fhnw-ip12-24vt/gletschery-docu/software(sad)/sad/12_glossary.adoc

== Glossar

[role="arc42help"]
****
.Inhalt
Die wesentlichen fachlichen und technischen Begriffe, die Stakeholder im Zusammenhang mit dem System verwenden.

Nutzen Sie das Glossar ebenfalls als Übersetzungsreferenz, falls Sie in mehrsprachigen Teams arbeiten.

.Motivation
Sie sollten relevante Begriffe klar definieren, so dass alle Beteiligten

* diese Begriffe identisch verstehen, und
* vermeiden, mehrere Begriffe für die gleiche Sache zu haben.

.Form
* Zweispaltige Tabelle mit <Begriff> und <Definition>
* Eventuell weitere Spalten mit Übersetzungen, falls notwendig.

.Weiterführende Informationen

Siehe https://docs.arc42.org/section-12/[Glossar] in der online-Dokumentation (auf Englisch!).

****

[cols="e,2e" options="header"]
|===
|Begriff |Definition

|<Begriff-1>
|<Definition-1>

|<Begriff-2
|<Definition-2>
|===
