fhnw-ip12-24vt/gletschery-docu/Files/generalImages/backgroundImage.png

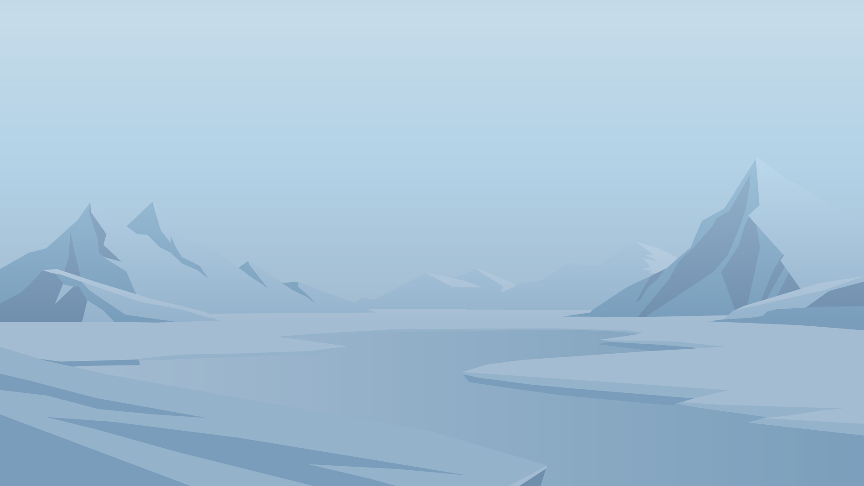
Files/generalImages/backgroundImage.png
