fhnw-ip12-24vt/gletschery-docu/Files/generalImages/englishFlag.png

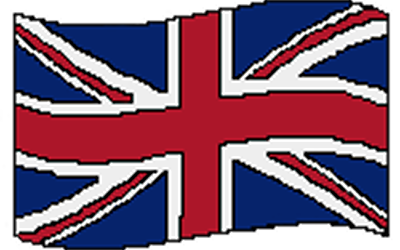
Files/generalImages/englishFlag.png
