fhnw-ip12-24vt/gletschery-docu/Files/generalImages/frenchFlag.png

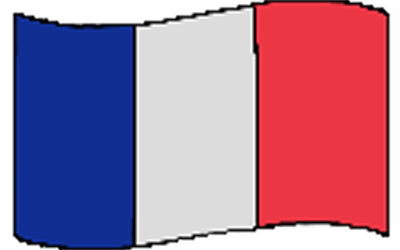
Files/generalImages/frenchFlag.png
