fhnw-ip12-24vt/gletschery-docu/Files/generalImages/germanFlag.png

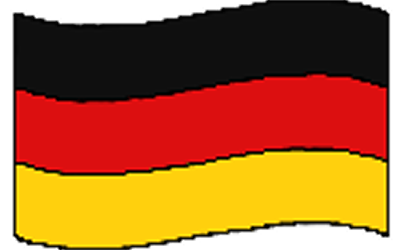
Files/generalImages/germanFlag.png
