fhnw-ip12-24vt/gletschery-docu/Files/generalImages/introductionDE.png

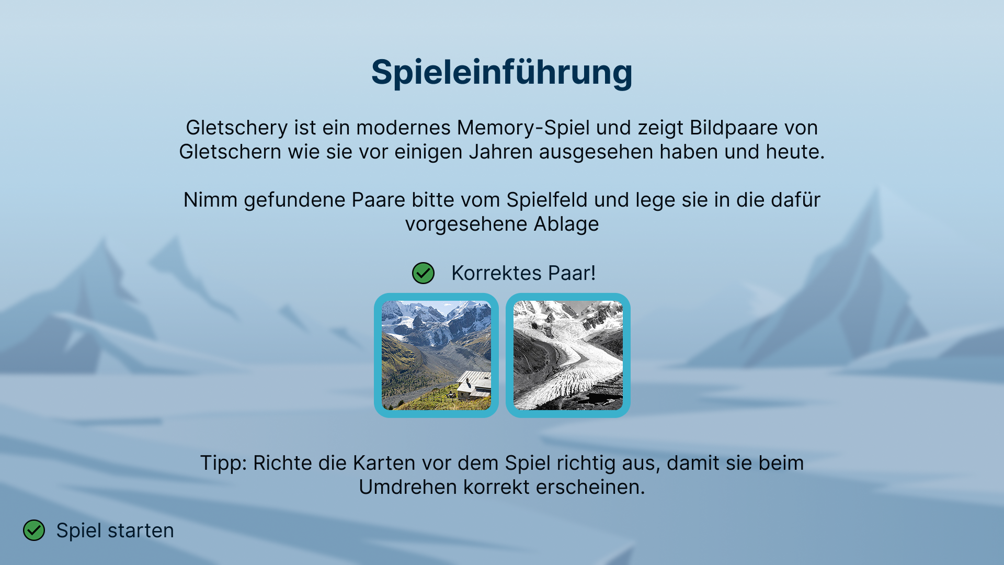
Files/generalImages/introductionDE.png
