fhnw-ip12-24vt/gletschery-docu/Files/generalImages/introductionEN.png

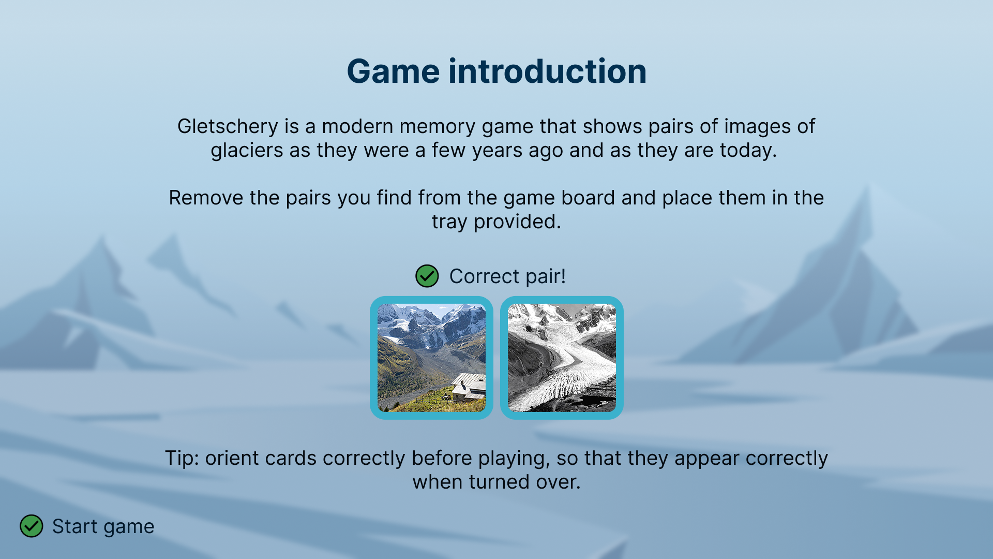
Files/generalImages/introductionEN.png
