fhnw-ip12-24vt/gletschery-docu/Files/generalImages/murmeltier.png

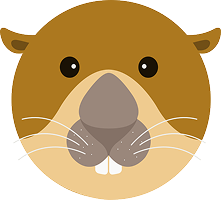
Files/generalImages/murmeltier.png
