fhnw-ip12-24vt/gletschery-docu/Files/generalImages/steinbock.png

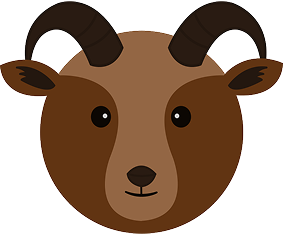
Files/generalImages/steinbock.png
