fhnw-ip12-24vt/gletschery-docu/Files/gletscherImages/Aletschgletscher-A.png

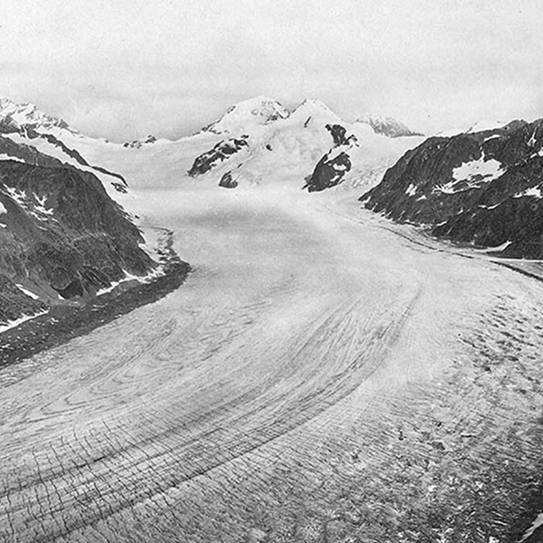
Files/gletscherImages/Aletschgletscher-A.png
