fhnw-ip12-24vt/gletschery-docu/Files/gletscherImages/Aletschgletscher-B.png

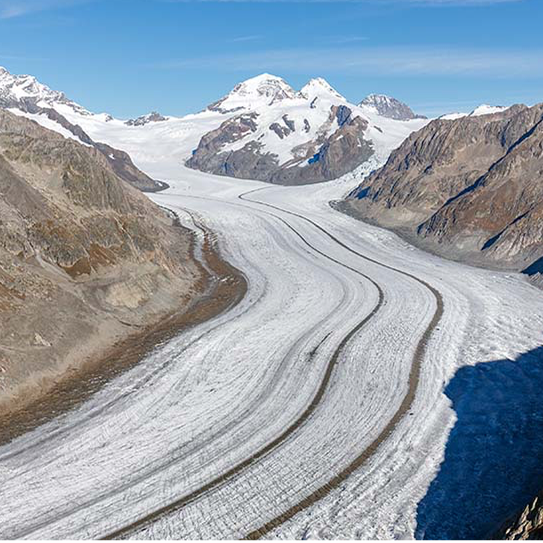
Files/gletscherImages/Aletschgletscher-B.png
