fhnw-ip12-24vt/gletschery-docu/Files/gletscherImages/Fieschergletscher-A.png

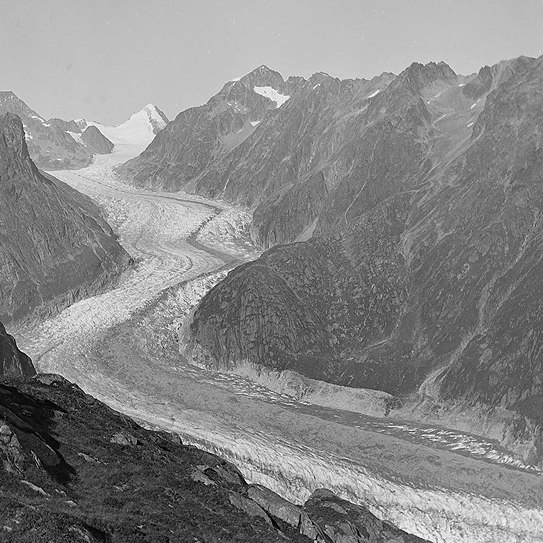
Files/gletscherImages/Fieschergletscher-A.png
