fhnw-ip12-24vt/gletschery-docu/Files/gletscherImages/Fieschergletscher-B.png

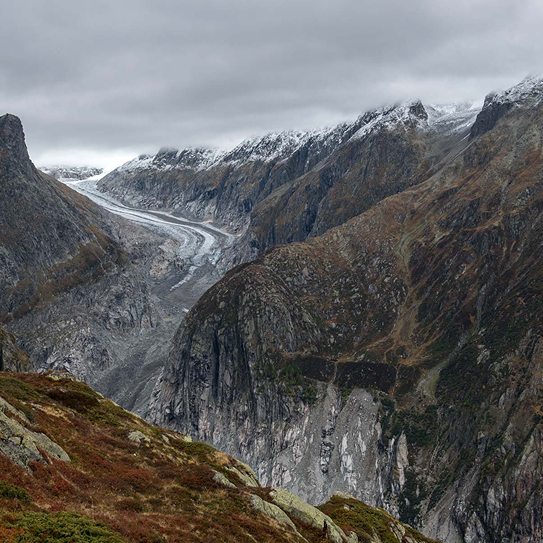
Files/gletscherImages/Fieschergletscher-B.png
