fhnw-ip12-24vt/gletschery-docu/Files/gletscherImages/Gornergletscher-A.png

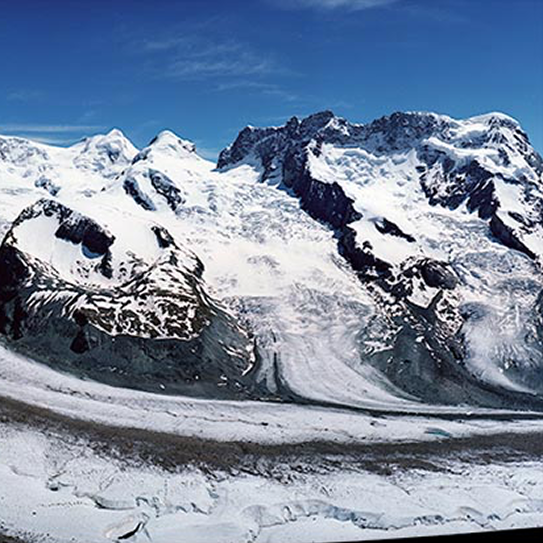
Files/gletscherImages/Gornergletscher-A.png
