fhnw-ip12-24vt/gletschery-docu/Files/gletscherImages/Gornergletscher-B.png

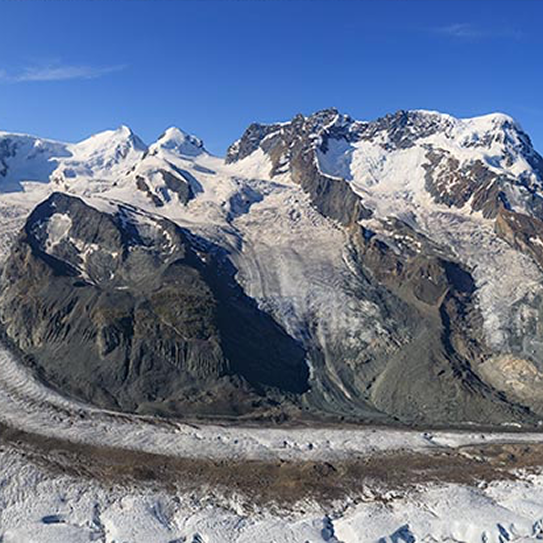
Files/gletscherImages/Gornergletscher-B.png
