fhnw-ip12-24vt/gletschery-docu/Files/gletscherImages/Persgletscher-A.png

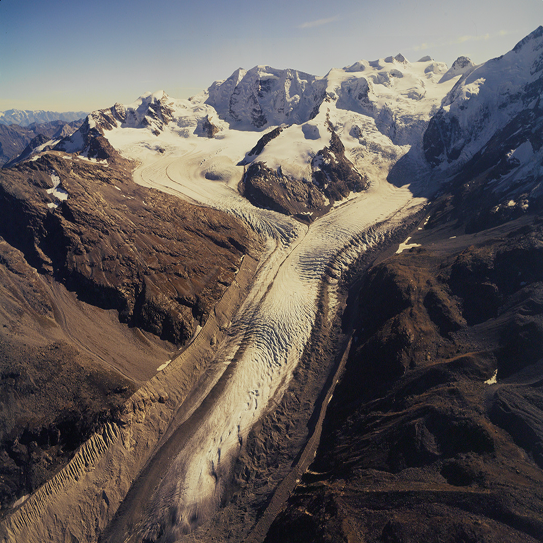
Files/gletscherImages/Persgletscher-A.png
