fhnw-ip12-24vt/gletschery-docu/Files/gletscherImages/Persgletscher-B.png

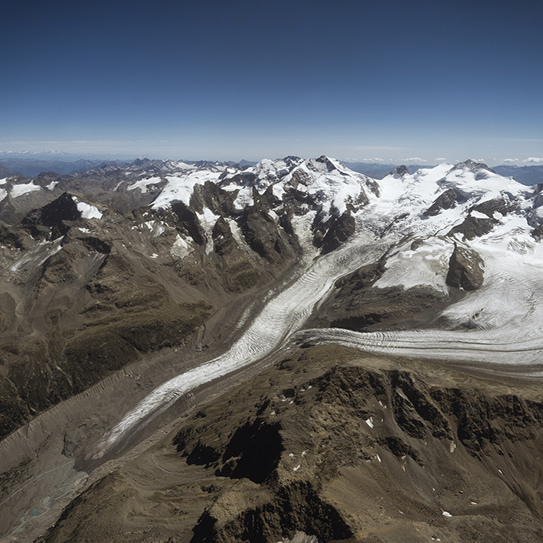
Files/gletscherImages/Persgletscher-B.png
