fhnw-ip12-24vt/gletschery-docu/Files/gletscherImages/Pizolgletscher-A.png

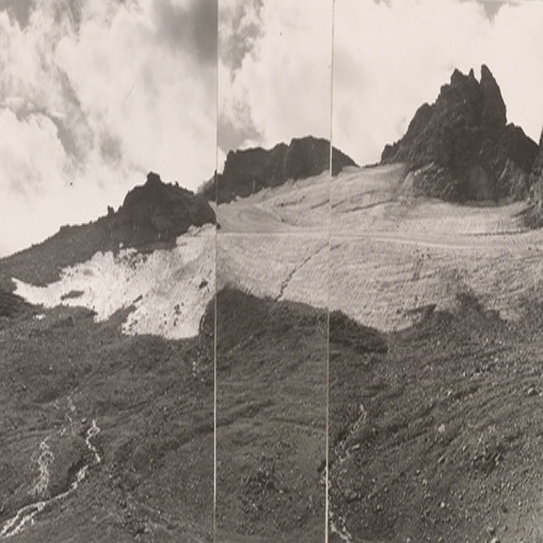
Files/gletscherImages/Pizolgletscher-A.png
