fhnw-ip12-24vt/gletschery-docu/Files/gletscherImages/Pizolgletscher-B.png

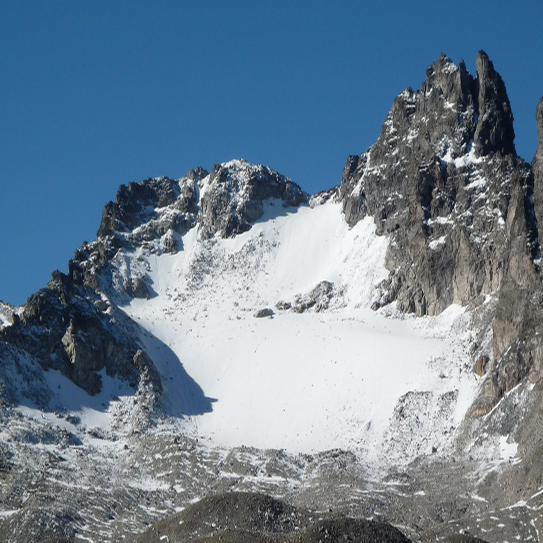
Files/gletscherImages/Pizolgletscher-B.png
