fhnw-ip12-24vt/gletschery-docu/Files/gletscherImages/Rhonegletscher-A.png

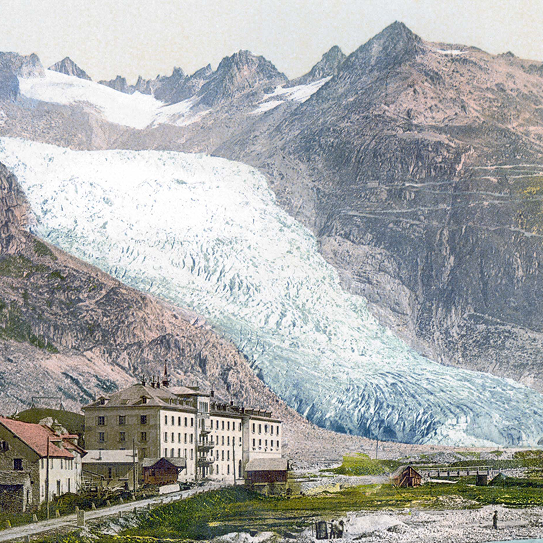
Files/gletscherImages/Rhonegletscher-A.png
