fhnw-ip12-24vt/gletschery-docu/Files/gletscherImages/Rhonegletscher-B.png

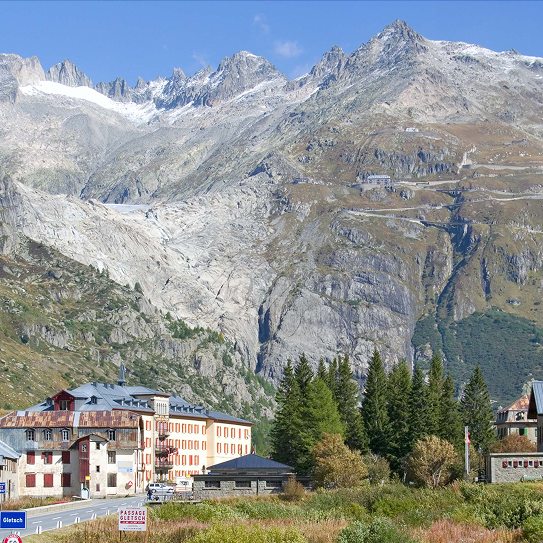
Files/gletscherImages/Rhonegletscher-B.png
