fhnw-ip12-24vt/gletschery-docu/Files/gletscherImages/Riedgletscher-A.png

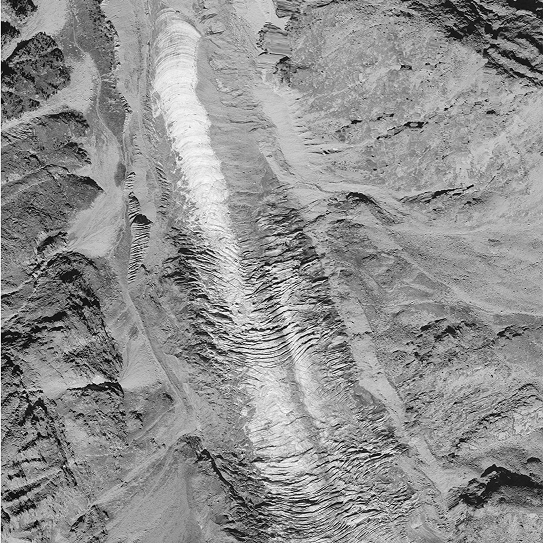
Files/gletscherImages/Riedgletscher-A.png
