fhnw-ip12-24vt/gletschery-docu/Files/gletscherImages/Riedgletscher-B.png

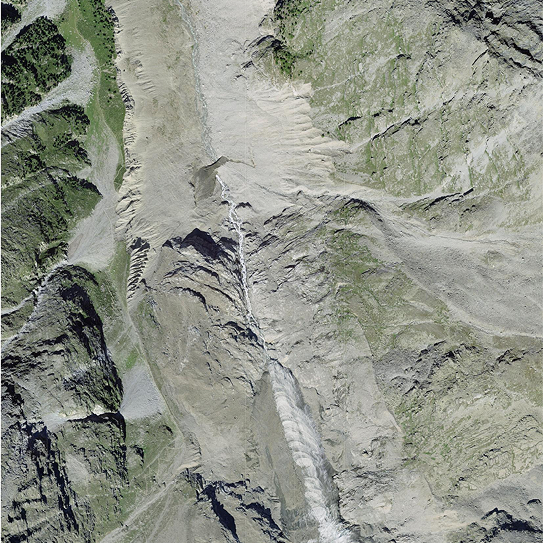
Files/gletscherImages/Riedgletscher-B.png
