fhnw-ip12-24vt/gletschery-docu/Files/gletscherImages/Roseggletscher-A.png

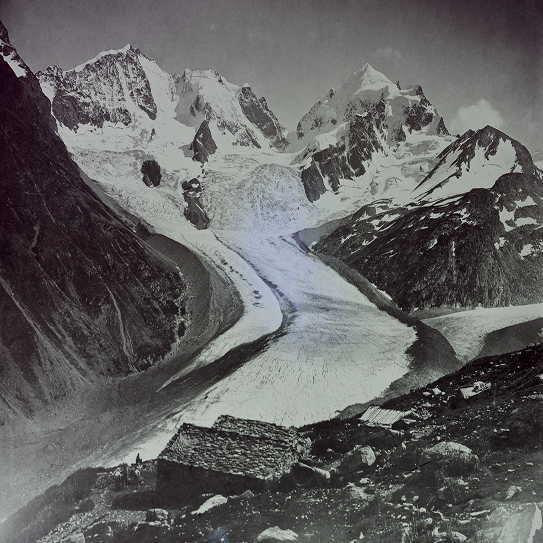
Files/gletscherImages/Roseggletscher-A.png
