fhnw-ip12-24vt/gletschery-docu/Files/gletscherImages/Roseggletscher-B.png

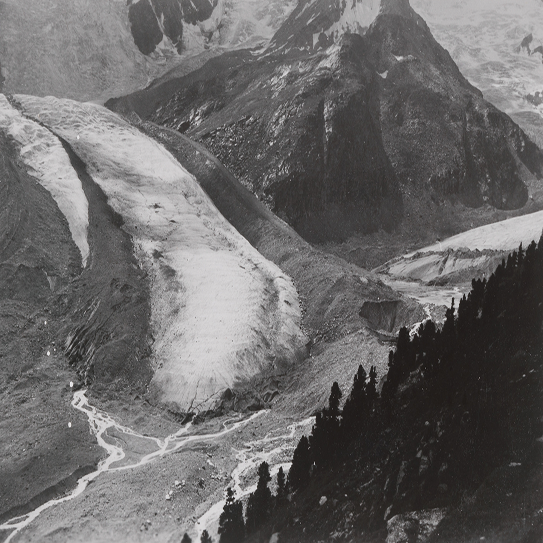
Files/gletscherImages/Roseggletscher-B.png
