fhnw-ip12-24vt/gletschery-docu/Files/gletscherImages/Tiefengletscher-A.png

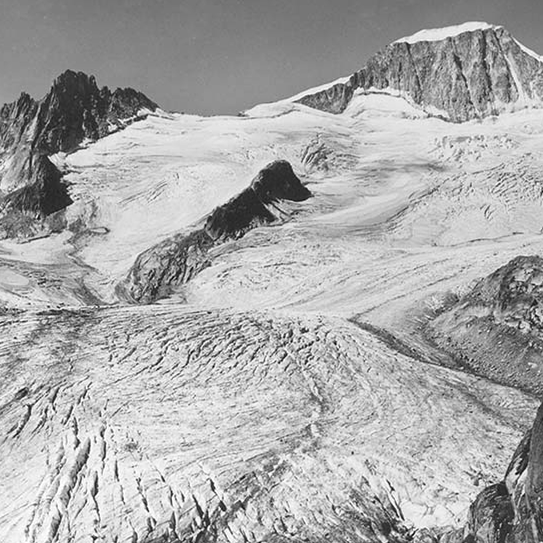
Files/gletscherImages/Tiefengletscher-A.png
