fhnw-ip12-24vt/gletschery-docu/Files/gletscherImages/Tiefengletscher-B.png

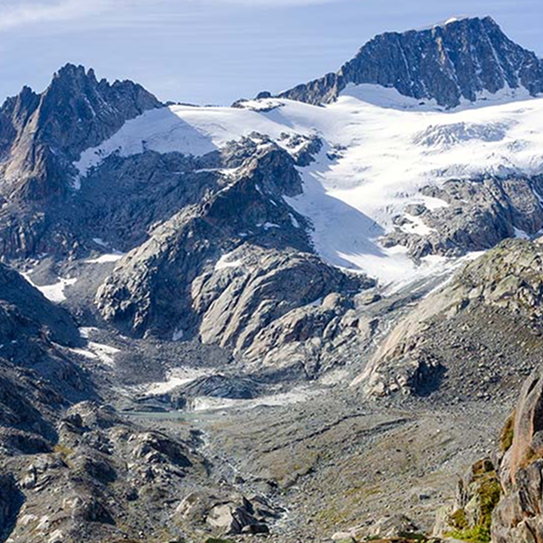
Files/gletscherImages/Tiefengletscher-B.png
