fhnw-ip12-24vt/gletschery-docu/Files/gletscherImages/Trientgletscher-A.png

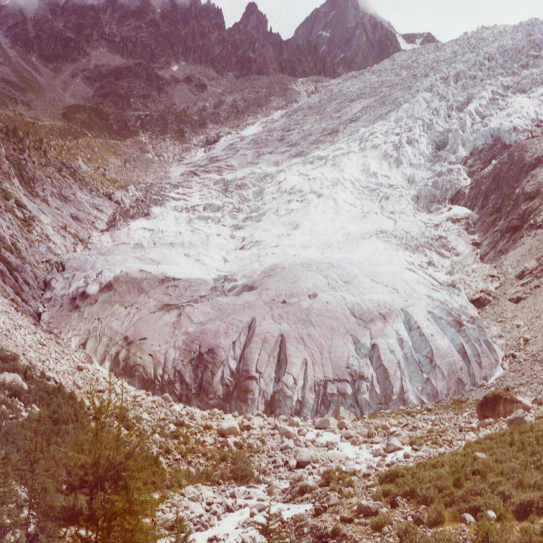
Files/gletscherImages/Trientgletscher-A.png
