fhnw-ip12-24vt/gletschery-docu/Files/gletscherImages/Trientgletscher-B.png

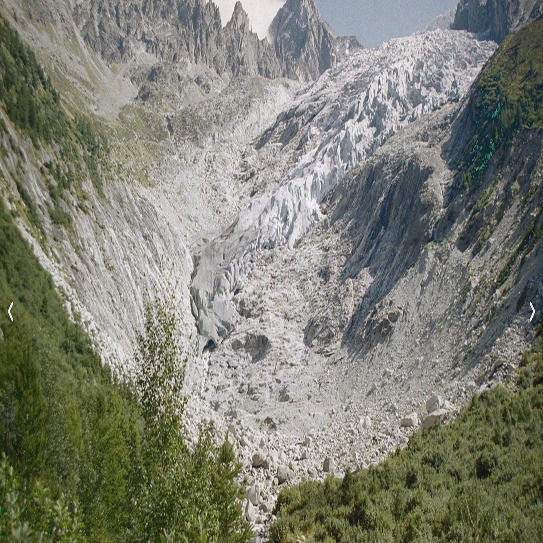
Files/gletscherImages/Trientgletscher-B.png
