fhnw-ip12-24vt/gletschery-docu/Files/gletscherImages/Triftgletscher-A.png

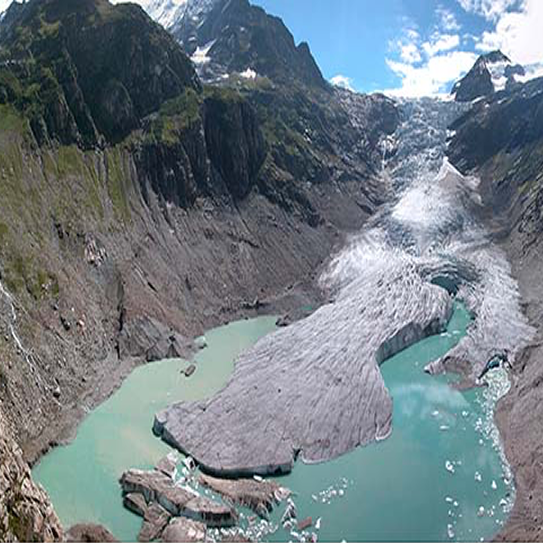
Files/gletscherImages/Triftgletscher-A.png
