fhnw-ip12-24vt/gletschery-docu/Files/gletscherImages/Triftgletscher-B.png

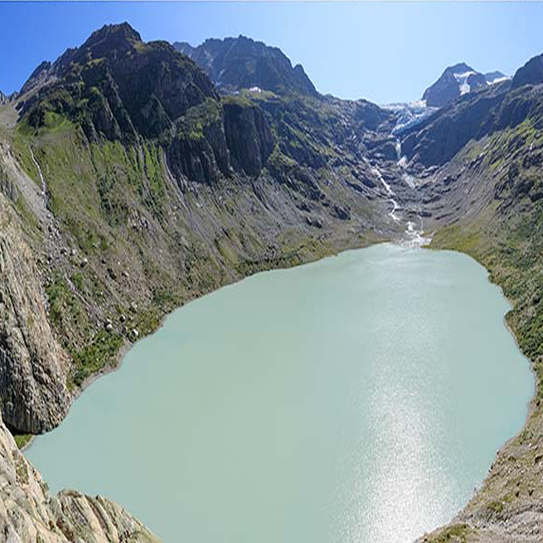
Files/gletscherImages/Triftgletscher-B.png
