fhnw-ip12-24vt/gletschery-docu/Files/gletscherImages/Tschierva-A.png

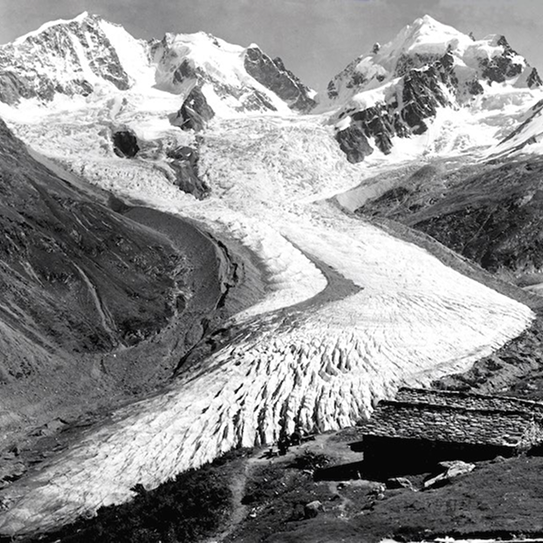
Files/gletscherImages/Tschierva-A.png
