fhnw-ip12-24vt/gletschery-docu/Files/gletscherImages/Tschierva-B.png

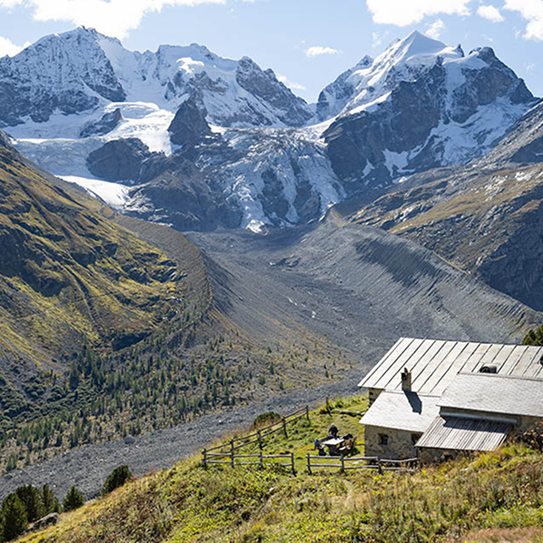
Files/gletscherImages/Tschierva-B.png
