fhnw-ip12-24vt/gletschery-docu/software(sad)/images/06-Flussdiagram-Run Methode.png

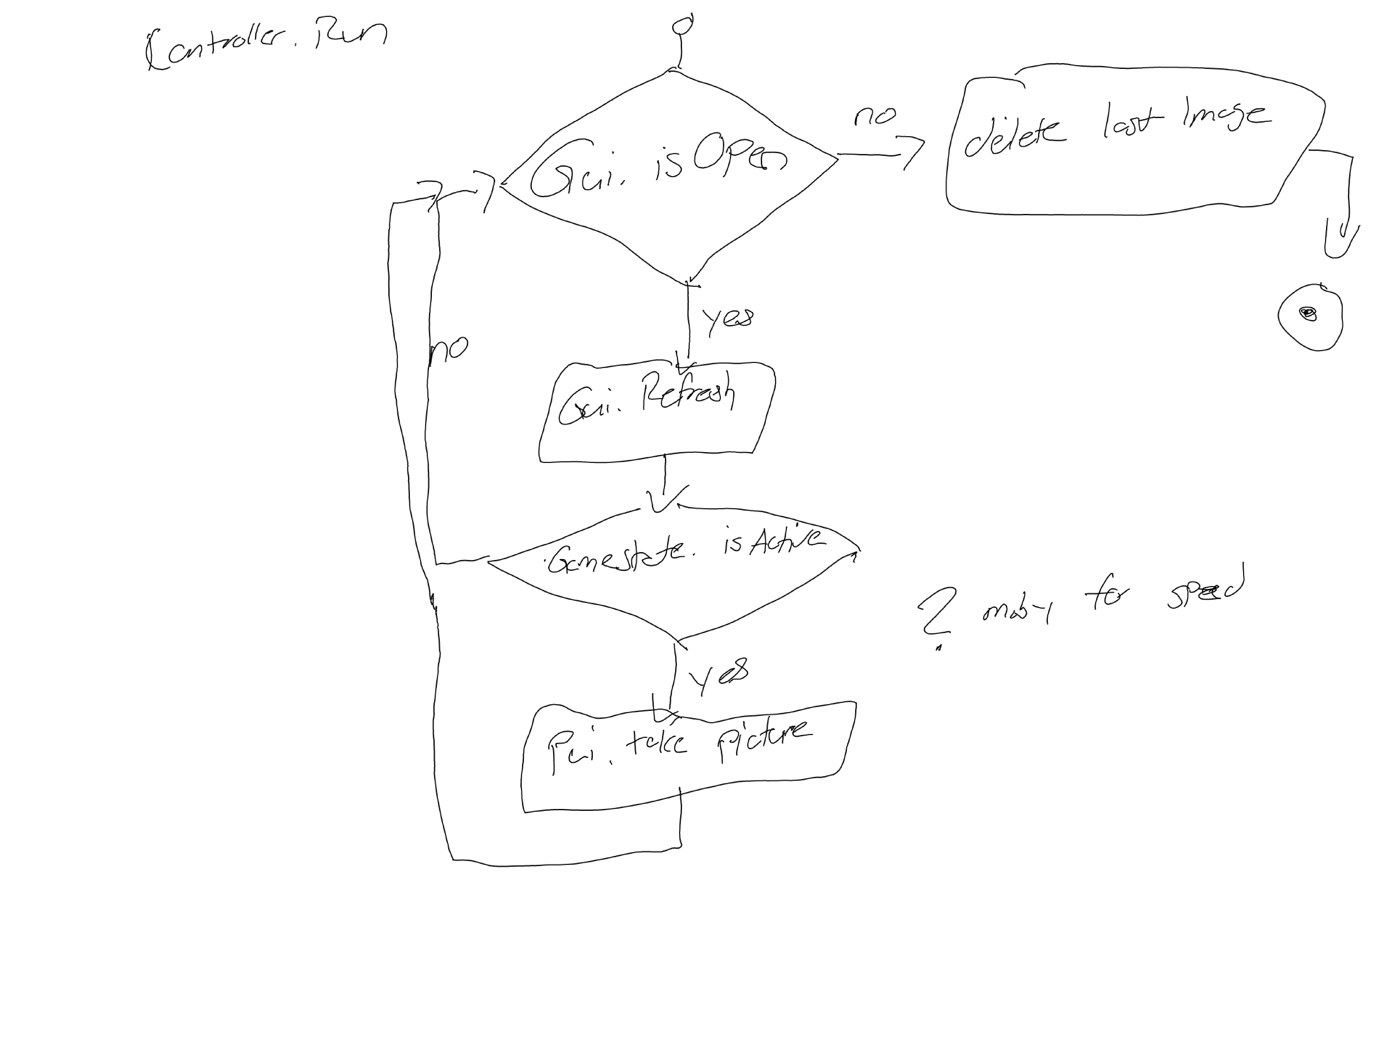
software(sad)/images/06-Flussdiagram-Run Methode.png
