fhnw-ip12-24vt/gletschery-docu/software(sad)/images/06-Sequenz Diagram Startup.png

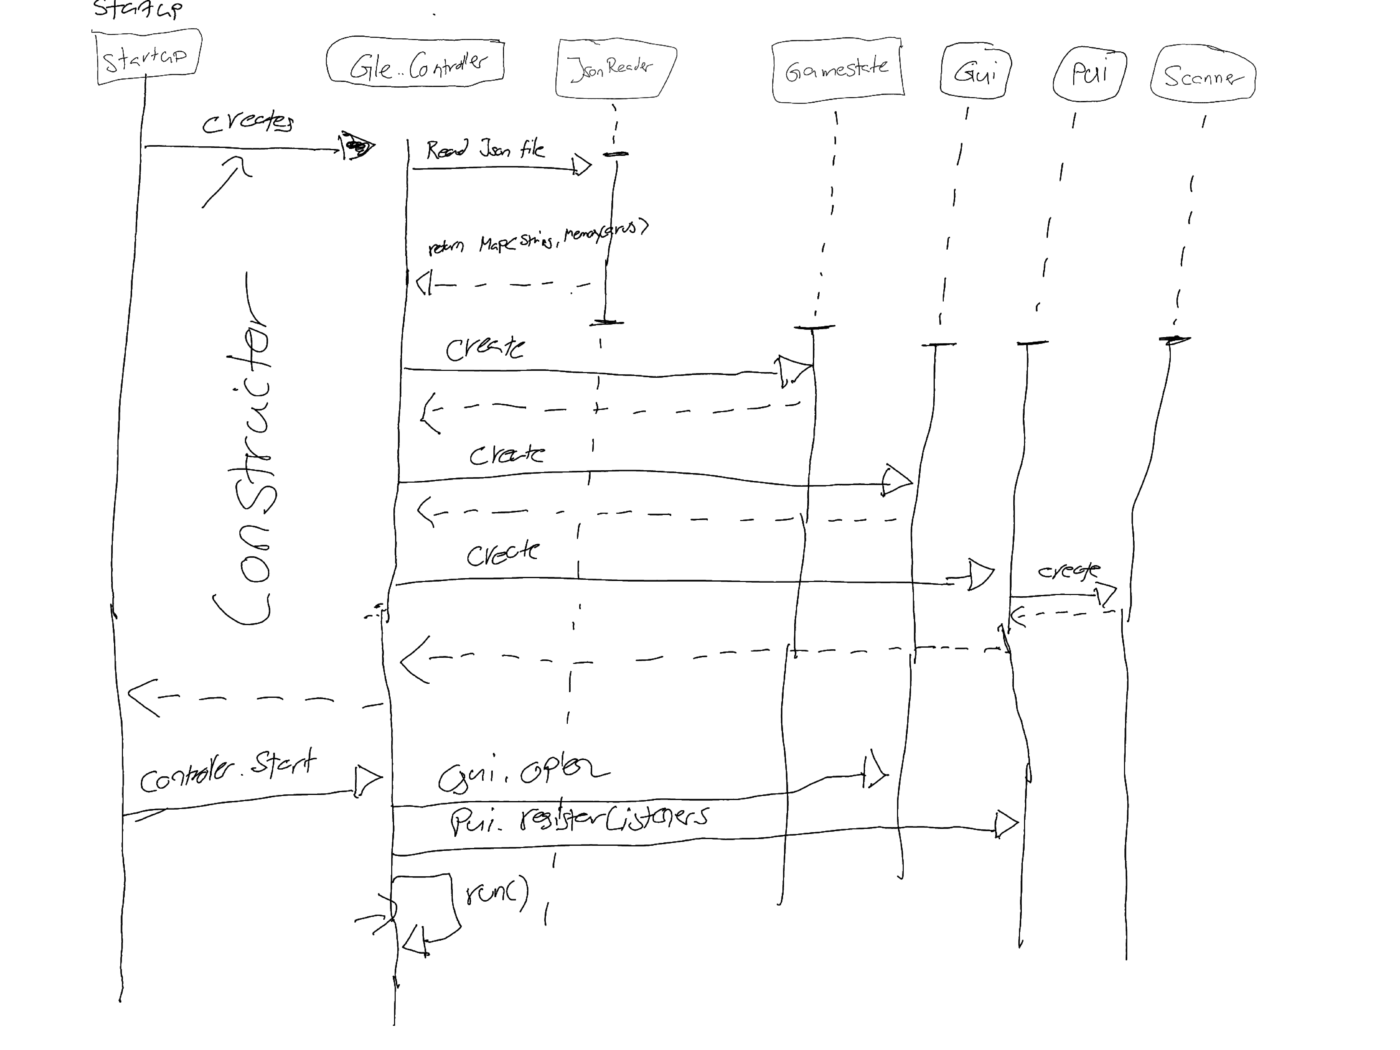
software(sad)/images/06-Sequenz Diagram Startup.png
