fhnw-ip12-24vt/gletschery-docu/software(sad)/images/06-Sequenz Diagram-Buttonpress(Scan).png

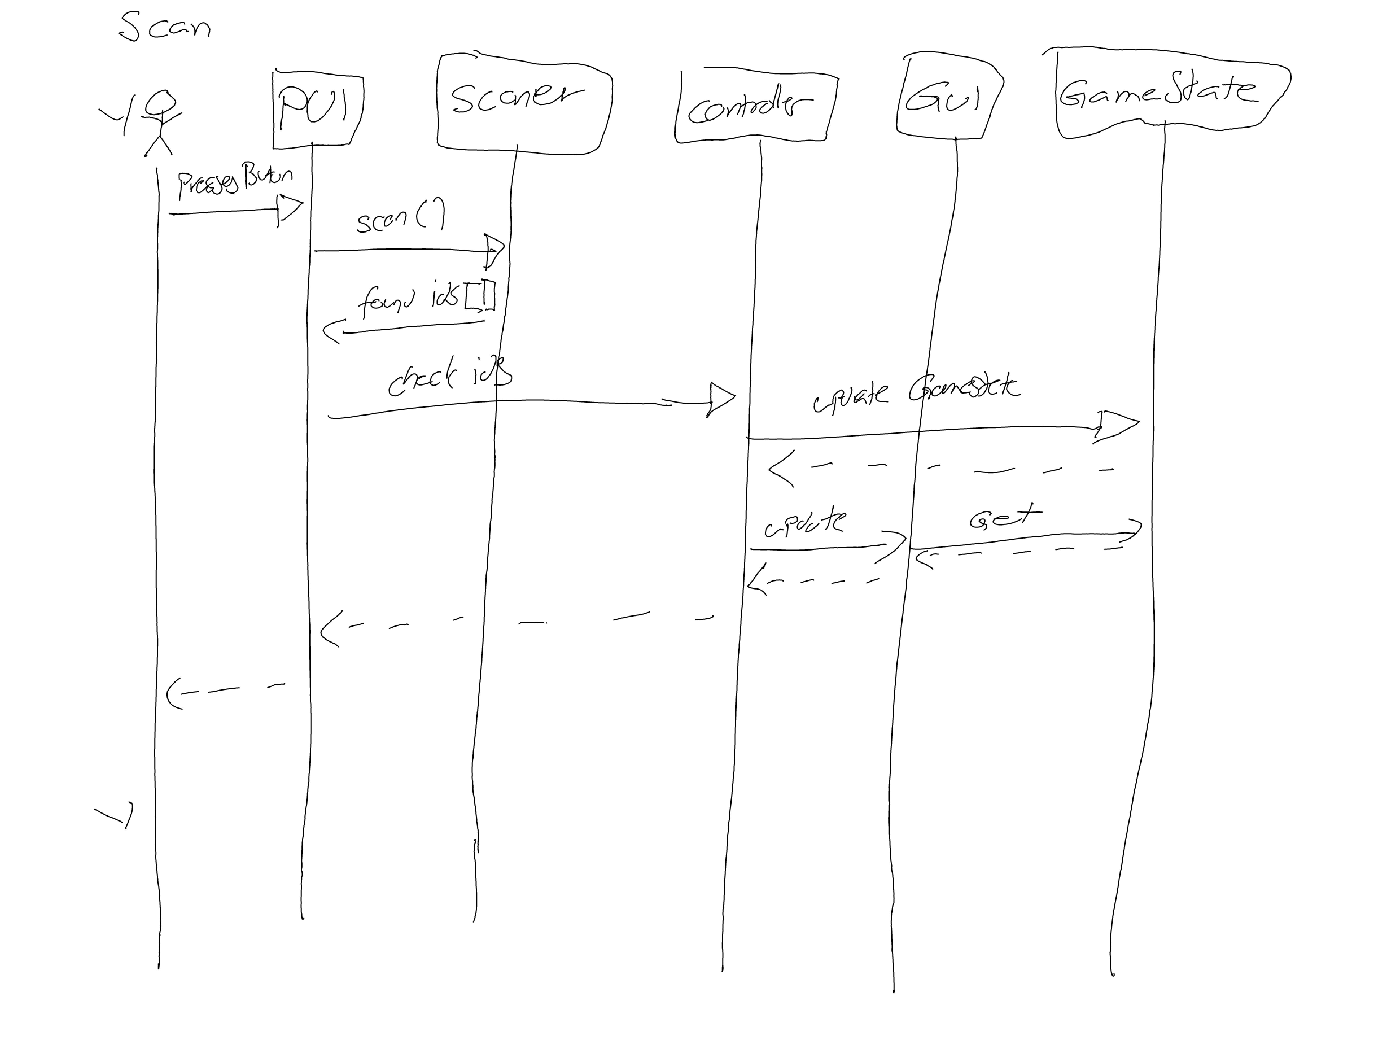
software(sad)/images/06-Sequenz Diagram-Buttonpress(Scan).png
