fhnw-ip12-24vt/gletschery-docu/software(sad)/images/06-Sequenz_Diagram_RedButton.png

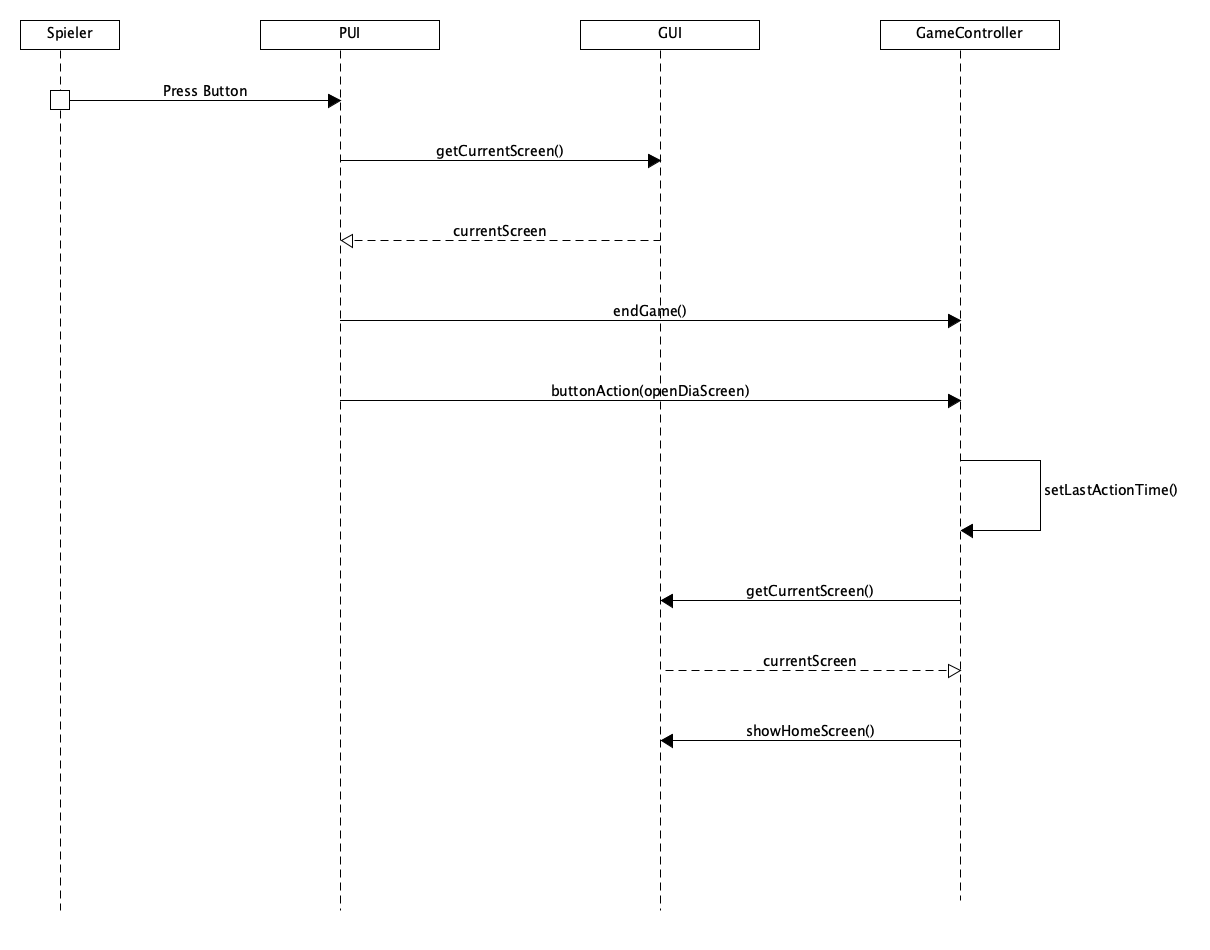
software(sad)/images/06-Sequenz_Diagram_RedButton.png
