fhnw-ip12-24vt/gletschery-docu/software(sad)/images/06_runtime_view_flussdiagramm.jpeg

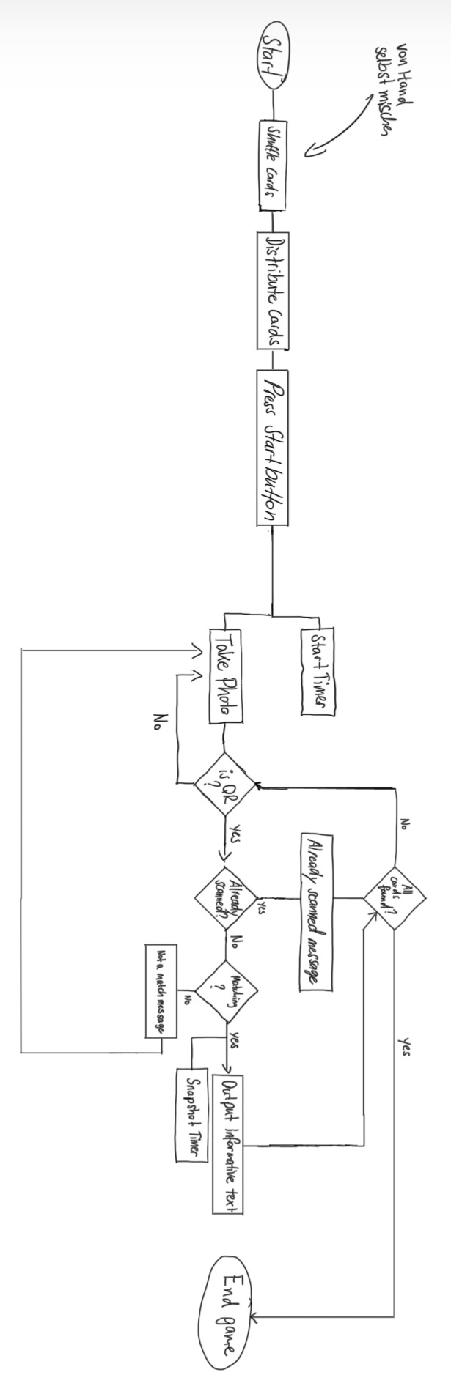
software(sad)/images/06_runtime_view_flussdiagramm.jpeg
