fhnw-ip12-24vt/gletschery-docu/software(sad)/images/10_quality_reqiurements_qualitytree_v2.png

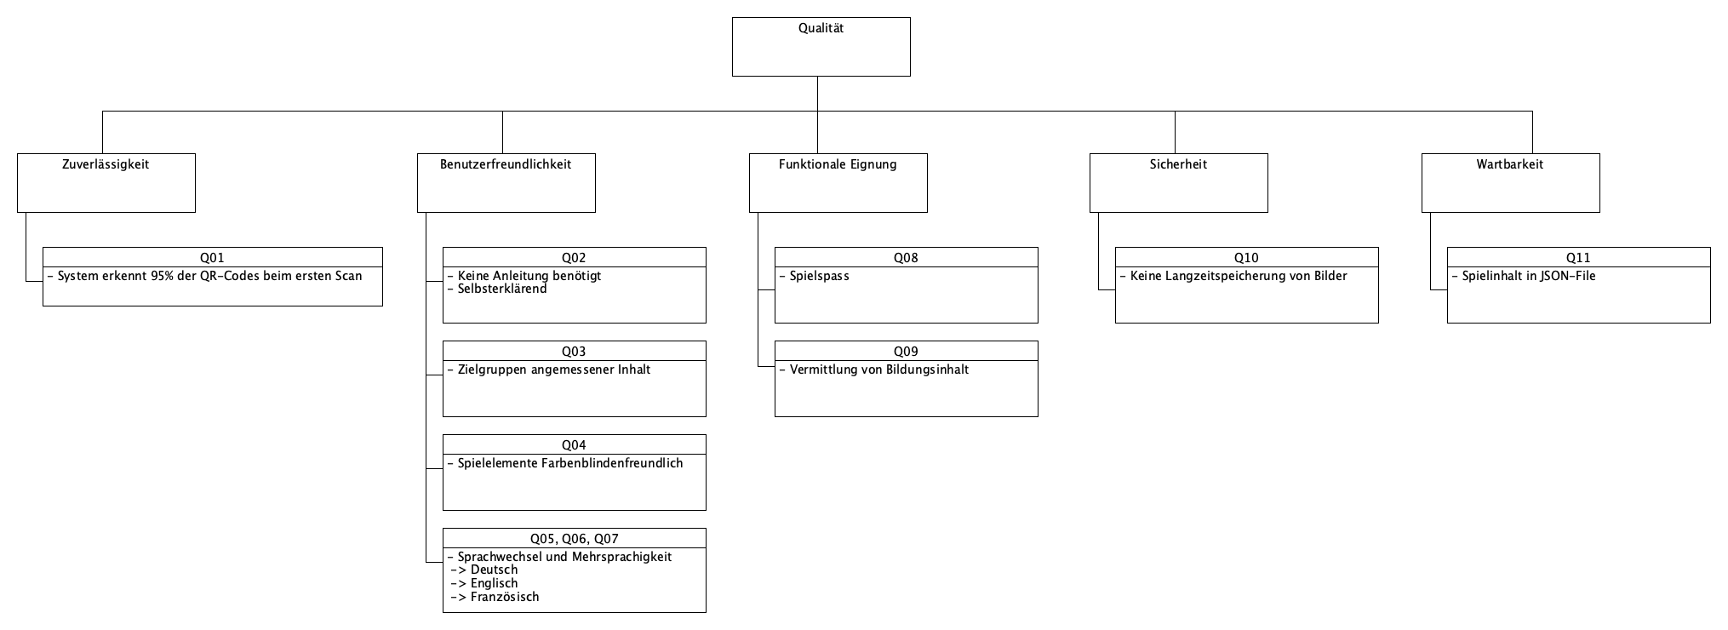
software(sad)/images/10_quality_reqiurements_qualitytree_v2.png
