fhnw-ip12-24vt/gletschery-docu/software(sad)/images/2024_HS24_GletscheryDemo_3.jpeg

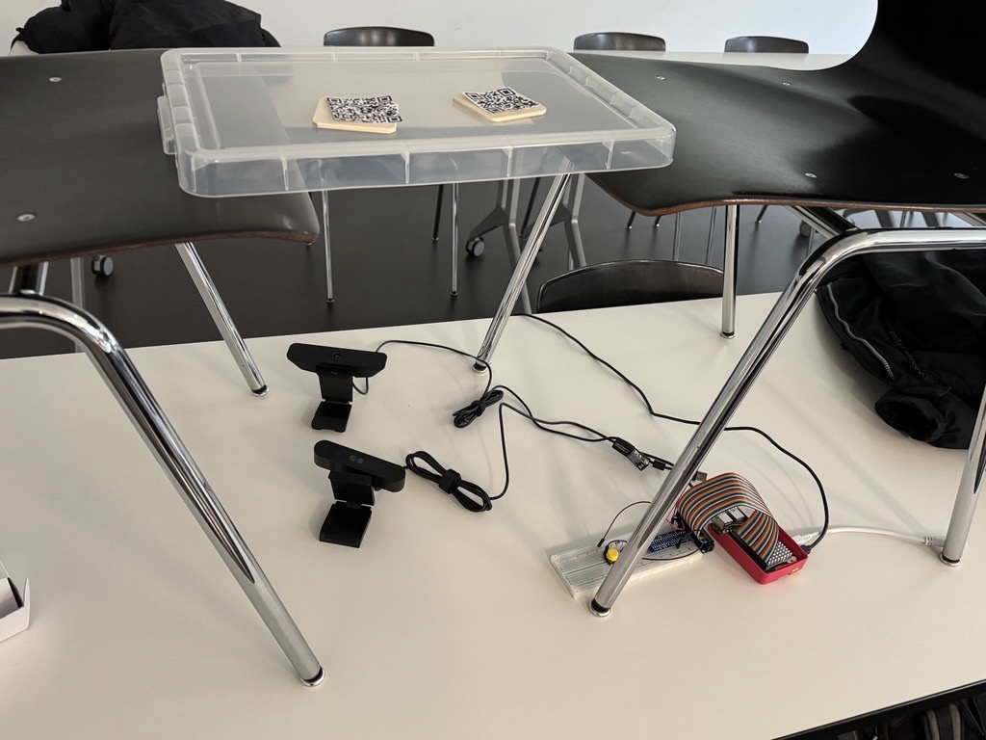
software(sad)/images/2024_HS24_GletscheryDemo_3.jpeg
