fhnw-ip12-24vt/gletschery-docu/software(sad)/images/2024_HS_GletscheryDemo_1.jpeg

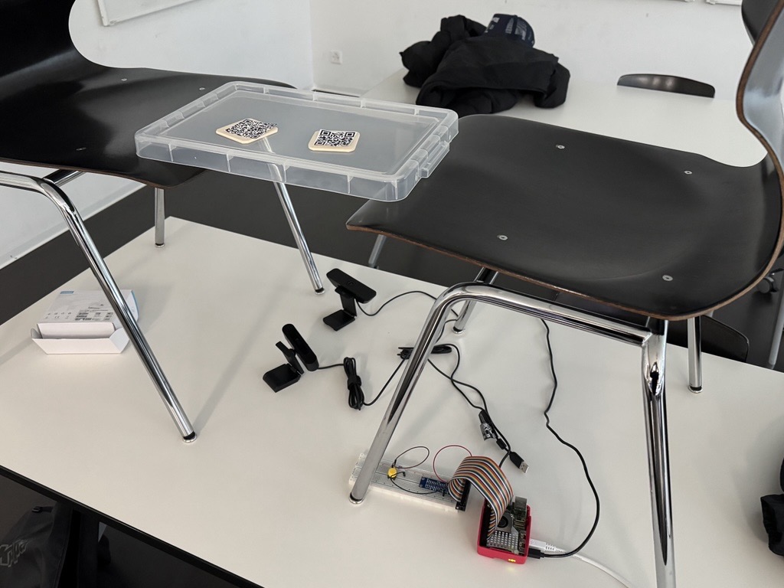
software(sad)/images/2024_HS_GletscheryDemo_1.jpeg
