fhnw-ip12-24vt/gletschery-docu/software(sad)/images/image_piecam_cable.png

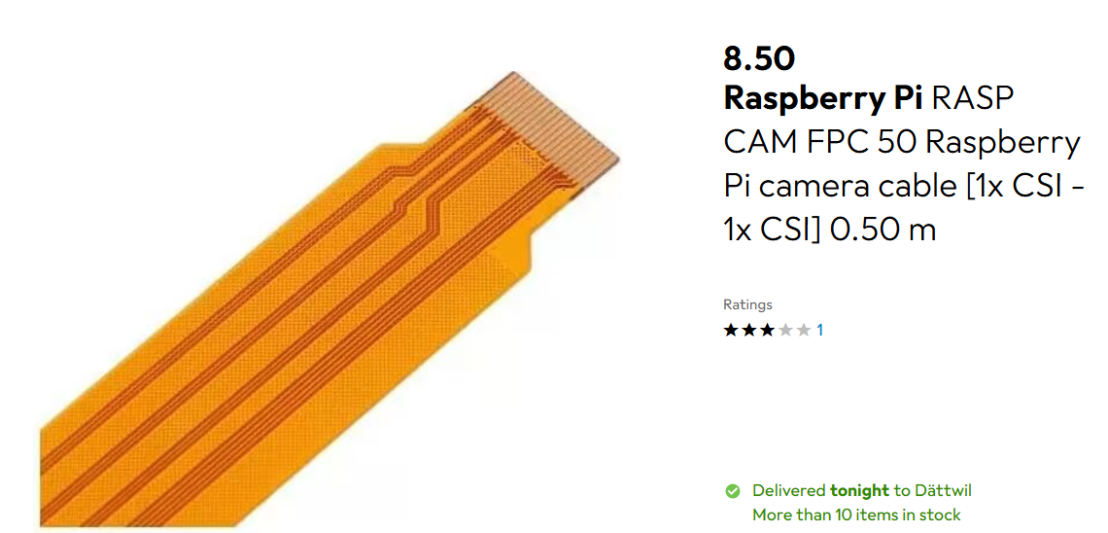
software(sad)/images/image_piecam_cable.png
