fhnw-ip12-24vt/gletschery-docu/hardware/Prototype/MemoryCards/3D_Files/memory-cards-v3 60x60x7.stl

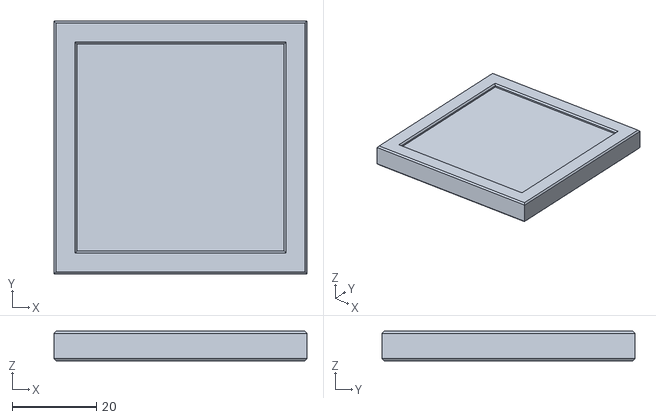
[picture p130: CAD file, 2025-06-06]
hardware/Prototype/MemoryCards/3D_Files/memory-cards-v3 60x60x7.stl
60.0 x 60.0 x 7.00
