fhnw-ip12-24vt/gletschery-docu/Files/generalImages/instruction.png

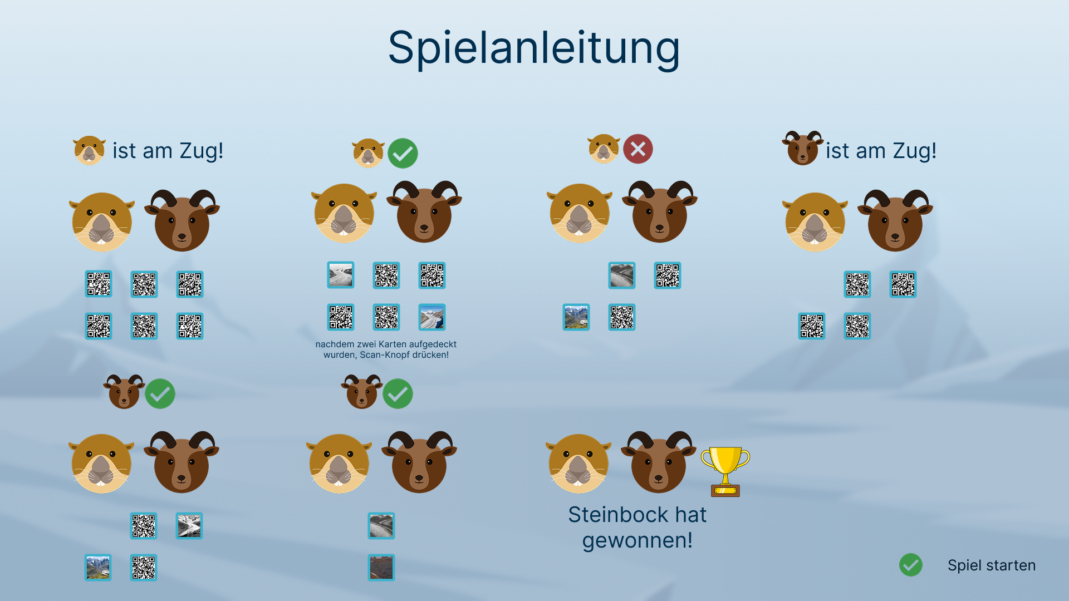
Files/generalImages/instruction.png
