fhnw-ip12-24vt/gletschery-docu/Files/generalImages/instructionDE.png

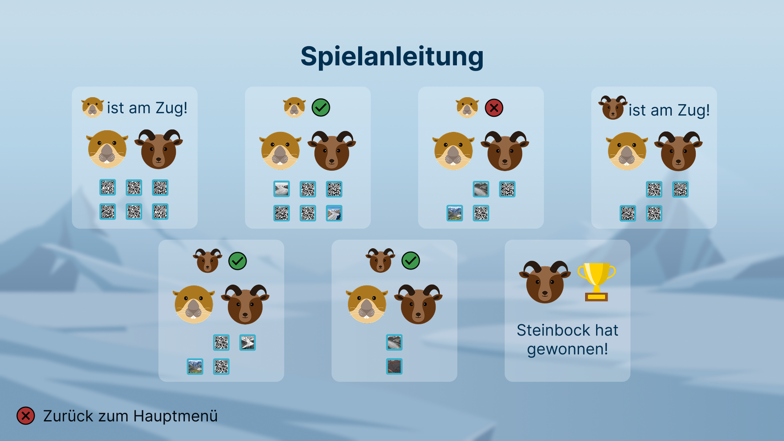
Files/generalImages/instructionDE.png
