fhnw-ip12-24vt/gletschery-docu/Files/generalImages/instructionEN.png

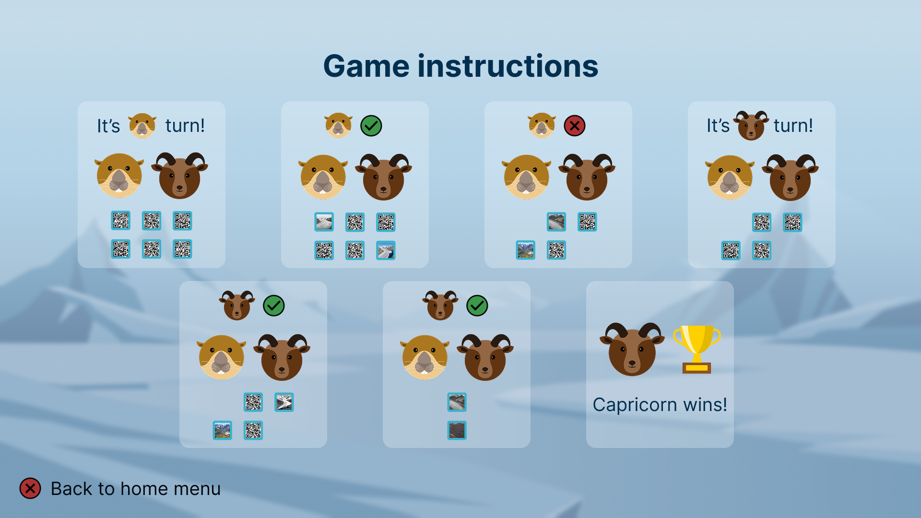
Files/generalImages/instructionEN.png
