fhnw-ip12-24vt/gletschery-docu/testing/RE-Tests/Qualitätsanforderungen/TC-32-0300.adoc

= Test Case Q03

|===
|Doc-ID: |TC-32-0300
|Datum: | 28.03.2025 und 09.04.2025
|===

== Beschreibung

Der Test soll sicherstellen, dass

- **Q03 - Benutzerfreundlichkeit: **Der Inhalt ist für die Zielgruppe angemessen und verständlich formuliert.

erfüllt werden kann.

== Bemerkung

Wird als Teil des Usability Testings in xref:../../UX-Tests/TC-33-0100.adoc[TC-33-0100] und xref:../../UX-Tests/TC-33-0101.adoc[TC-33-0101] abgehandelt.
