fhnw-ip12-24vt/gletschery-docu/testing/RE-Tests/Funktionale Anforderungen/TC-32-0101.adoc

= Test Case F01.UC01

|===
|Doc-ID: |TC-32-0101
|Datum: | 14.05.2025
|Test durchgeführt durch: | Nora Ramos
|===

== Beschreibung

Der Test soll sicherstellen, dass

**F01.UC01 - Spielinformationen sehen**

erfüllt werden kann.

== Annahmen und Voraussetzungen

- Die Bildschirmausgabe ist implementiert und funktionstüchtig.
- Das Spiel ist korrekt mit Strom versorgt.
- Die Benutzeroberfläche ist vollständig geladen.

== Testdaten

- Spieleranzahl: 2
- Spielmodus: Multiplayer
- Eingabesystem: Buttons
- Spracheinstellung: Deutsch, Französisch, Englisch

== Auszuführende Schritte

. Stromzufuhr herstellen – das Spiel startet automatisch.
. Startmenü erscheint auf dem Bildschirm.
. Spieler*in drückt auf START
. Spieler*in klickt durch die Spieleinführung und erste Spielanweisung (Punktestand, Icon aktueller Spieler, Feedback: Spieler XY ist am Zug) erscheint.
. Spieler*in dreht zwei Karten um und drückt auf den Scan-Knopf
- *Kartenpaar ist korrekt:* Bildschirm zeigt Gletscherbilder mit grünem Rand, einen Fakt und angepassten Punktestand.
- *Kartenpaar ist falsch:* Bildschirm zeigt Gletscherbilder mit rotem Rand.
. Spieler*in setzt das Spiel fort, neuer Hinweis erscheint.

== Erwartetes Ergebnis

. Das Startmenü wird angezeigt.
. Bei Spielstart erscheint die Spieleinführung und der erste Hinweis. Punktestand ist auf 0 zurückgesetzt.
. Jede Aktion löst eine sichtbare Rückmeldung aus.
. Es werden Punktestand, aktueller Spieler und Gletscherinformationen korrekt angezeigt.

== Erzieltes Ergebnis

. Alle Informationen wurden wie erwartet angezeigt.
. Die Bildschirmreaktionen stimmen mit den Benutzeraktionen überein.
. Gletscherdaten wurden korrekt dargestellt.
.Spielerwechsel und Punktestand funktionierten zuverlässig.

== Bemerkungen

Test erfolgreich abgeschlossen. Keine funktionalen Abweichungen festgestellt.
